DorianKnight/EEPROM_Programmer/7SD_hat/Seven Segment Display/photos/v1_hat_1.png

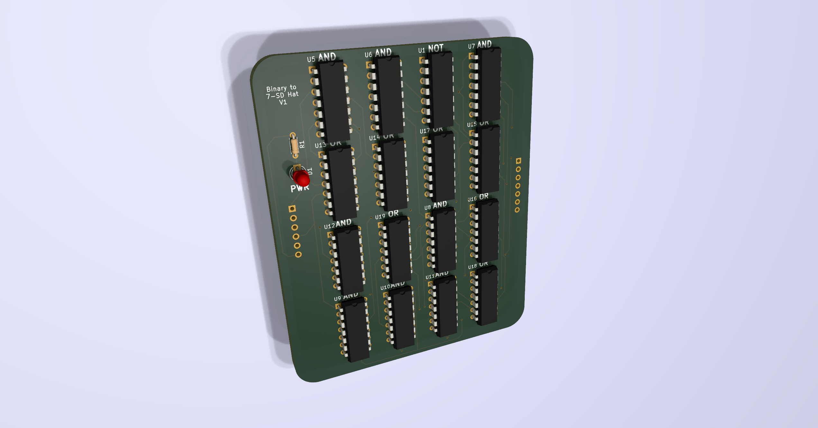
7SD_hat/Seven Segment Display/photos/v1_hat_1.png
